locnho/wifi-orp-monitor/images/IMG_5029.jpg

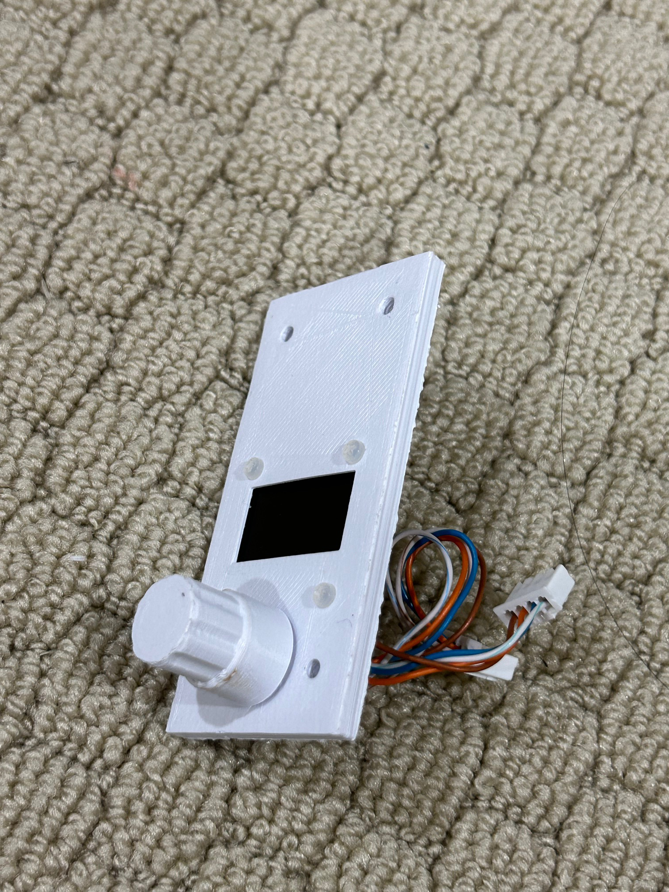
images/IMG_5029.jpg
